mj122333/TSCmikroklima/node/scheme/esp32_pins.PNG

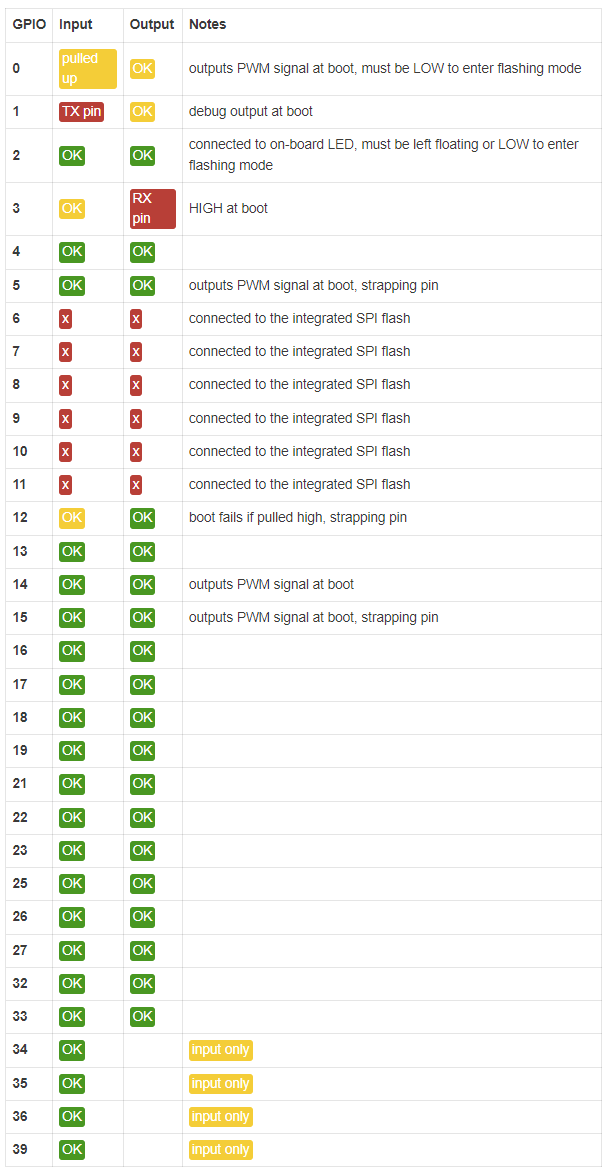
node/scheme/esp32_pins.PNG
