mj122333/TSCmikroklima/node/scheme/komponente/18b20.PNG

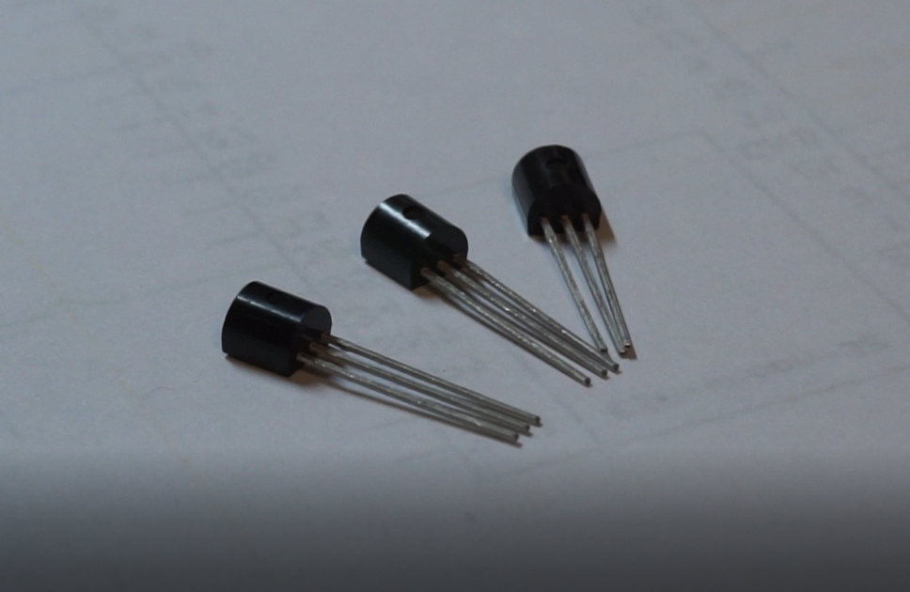
node/scheme/komponente/18b20.PNG
