mj122333/TSCmikroklima/node/scheme/komponente/baterija_18650.PNG

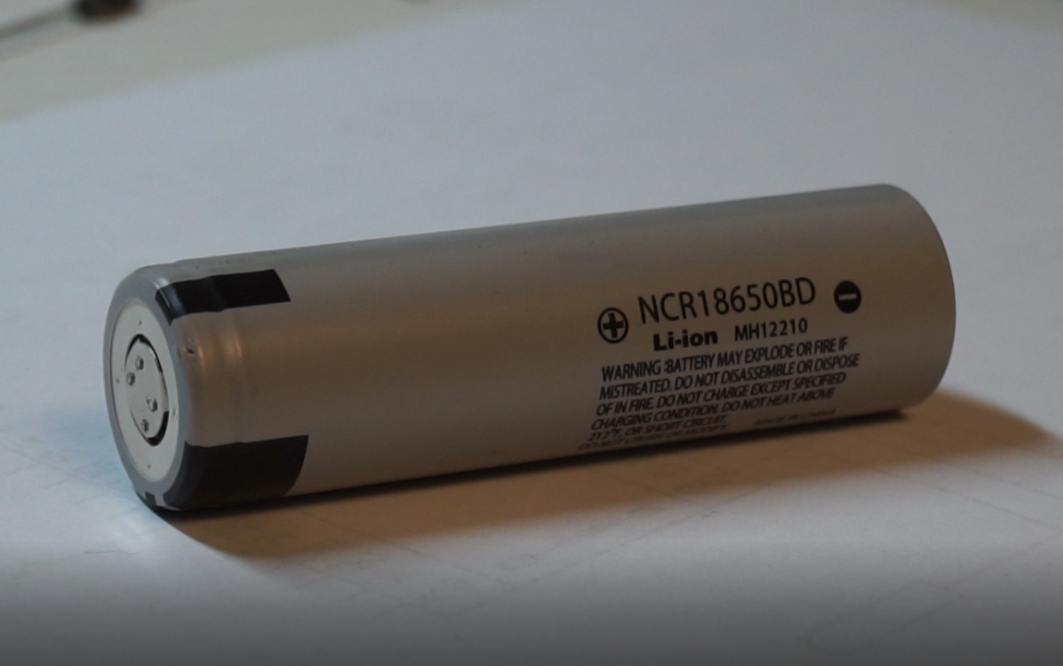
node/scheme/komponente/baterija_18650.PNG
