mj122333/TSCmikroklima/node/scheme/komponente/dioda.PNG

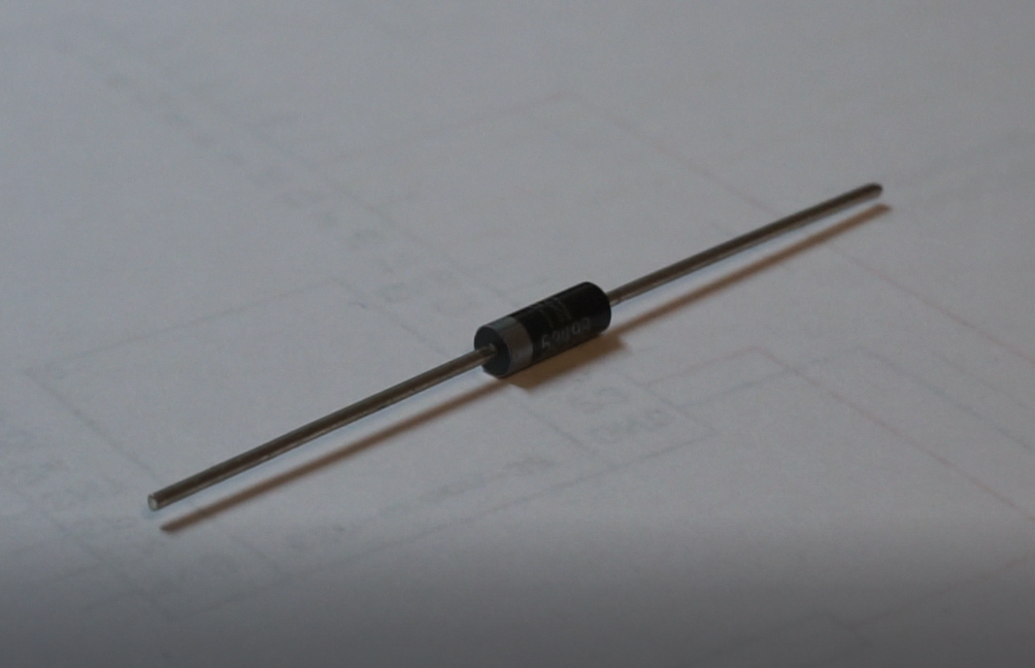
node/scheme/komponente/dioda.PNG
