mj122333/TSCmikroklima/node/scheme/komponente/esp32.PNG

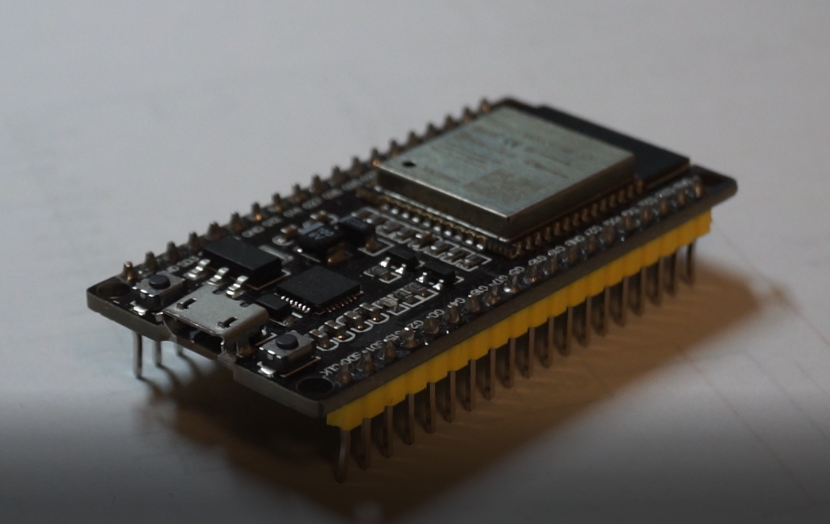
node/scheme/komponente/esp32.PNG
