mj122333/TSCmikroklima/node/scheme/komponente/hall.PNG

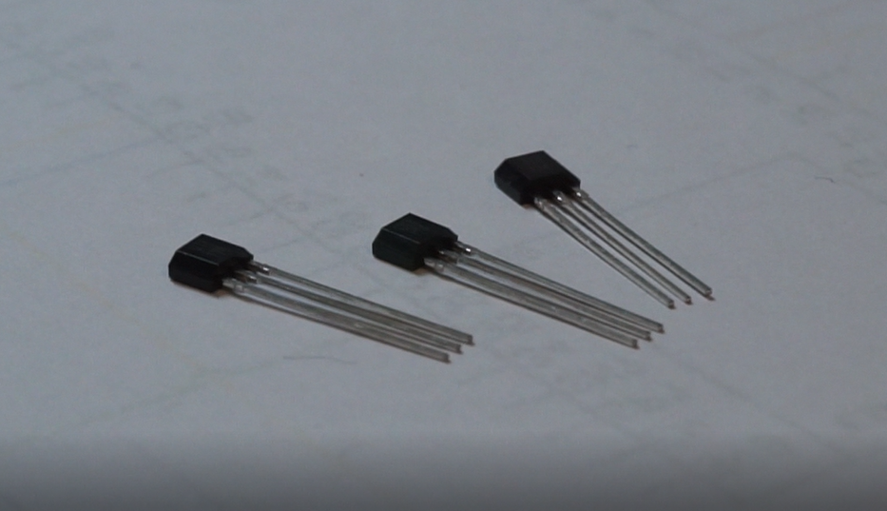
node/scheme/komponente/hall.PNG
