mj122333/TSCmikroklima/node/scheme/komponente/hall_u_akciji.PNG

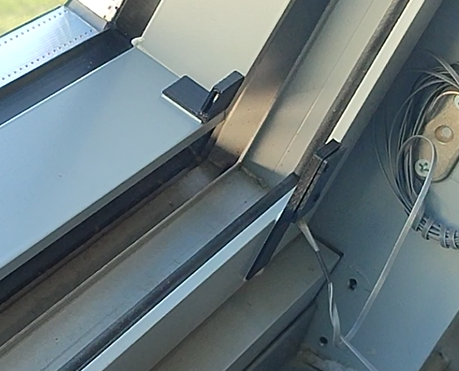
node/scheme/komponente/hall_u_akciji.PNG
