mj122333/TSCmikroklima/node/scheme/komponente/kuciste.PNG

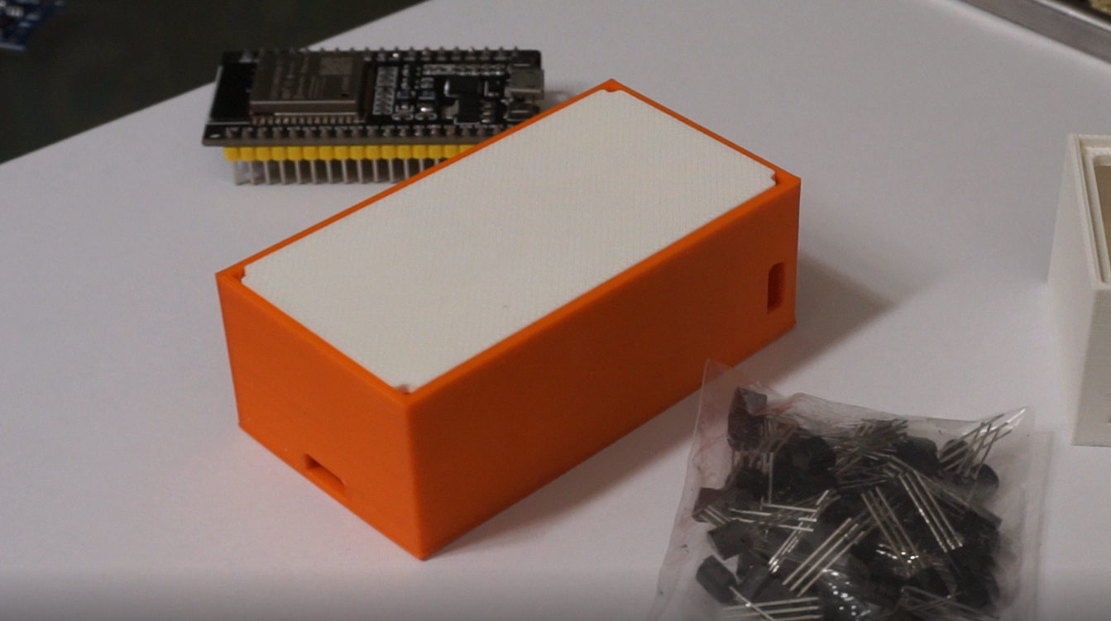
node/scheme/komponente/kuciste.PNG
