mj122333/TSCmikroklima/node/scheme/komponente/otpornici.PNG

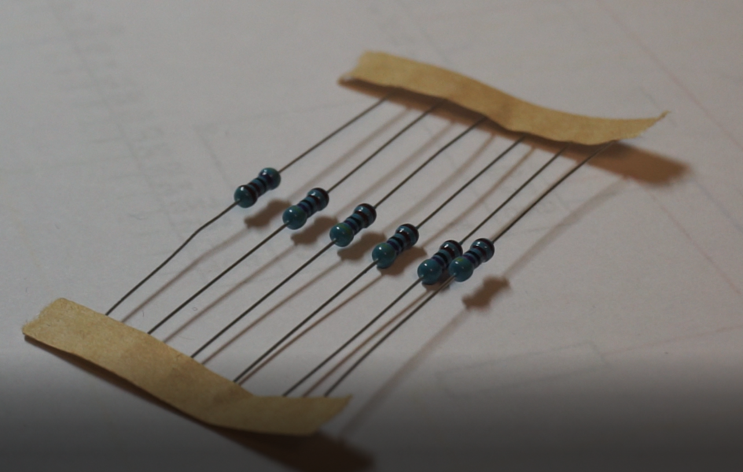
node/scheme/komponente/otpornici.PNG
