mj122333/TSCmikroklima/node/scheme/komponente/punjac.PNG

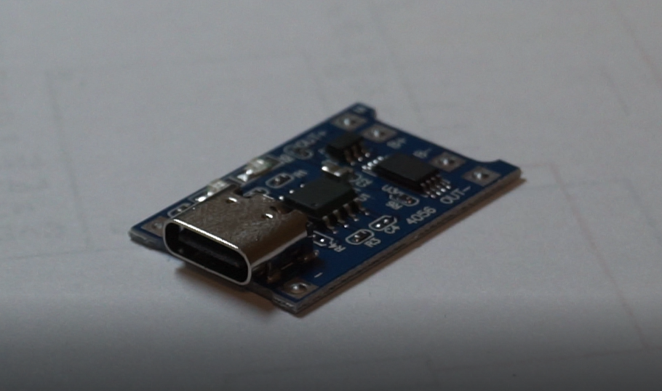
node/scheme/komponente/punjac.PNG
