mj122333/TSCmikroklima/node/scheme/scheme_3_2.PNG

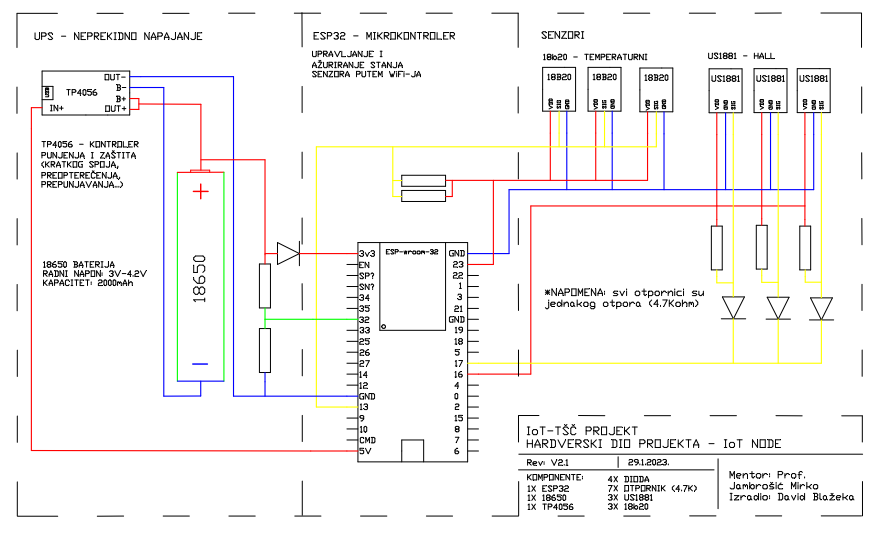
node/scheme/scheme_3_2.PNG
