mj122333/TSCmikroklima/node/scheme/underside_pinView.jpg

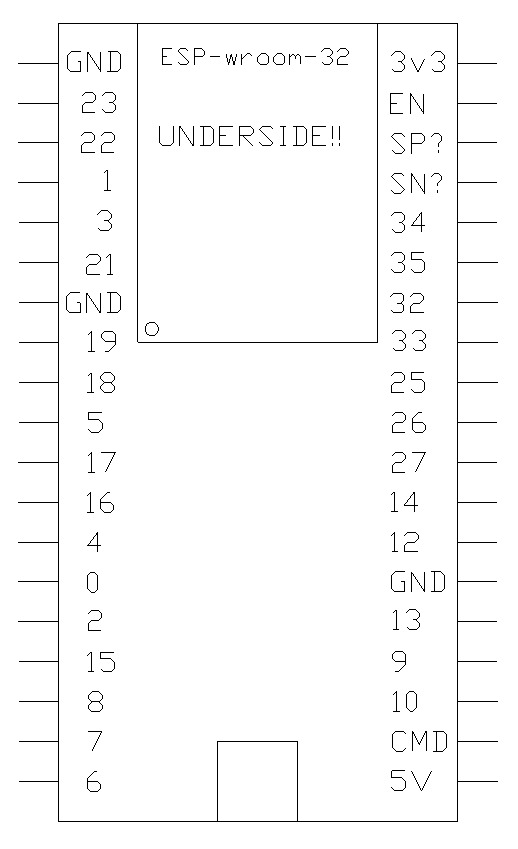
node/scheme/underside_pinView.jpg
