mj122333/TSCmikroklima/server/slike/tlocrt-kat-hodnik-tv.png

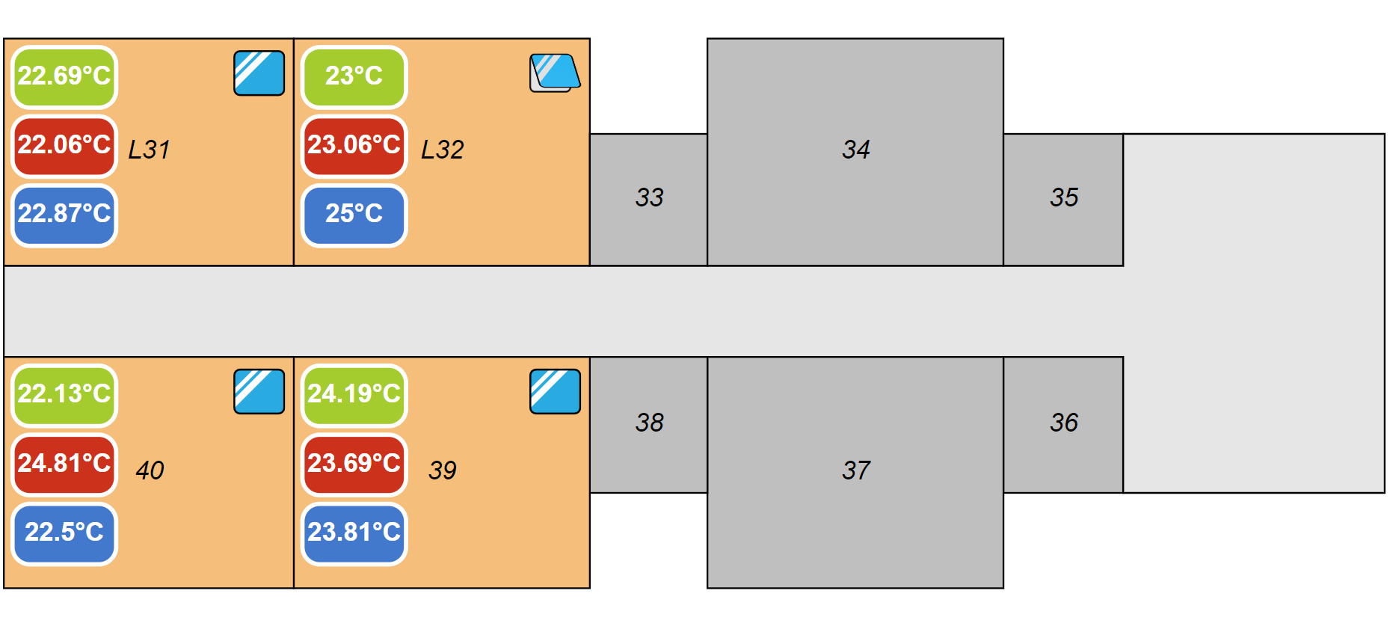
server/slike/tlocrt-kat-hodnik-tv.png
