mj122333/TSCmikroklima/server/slike/tlocrt-kat-tv.png

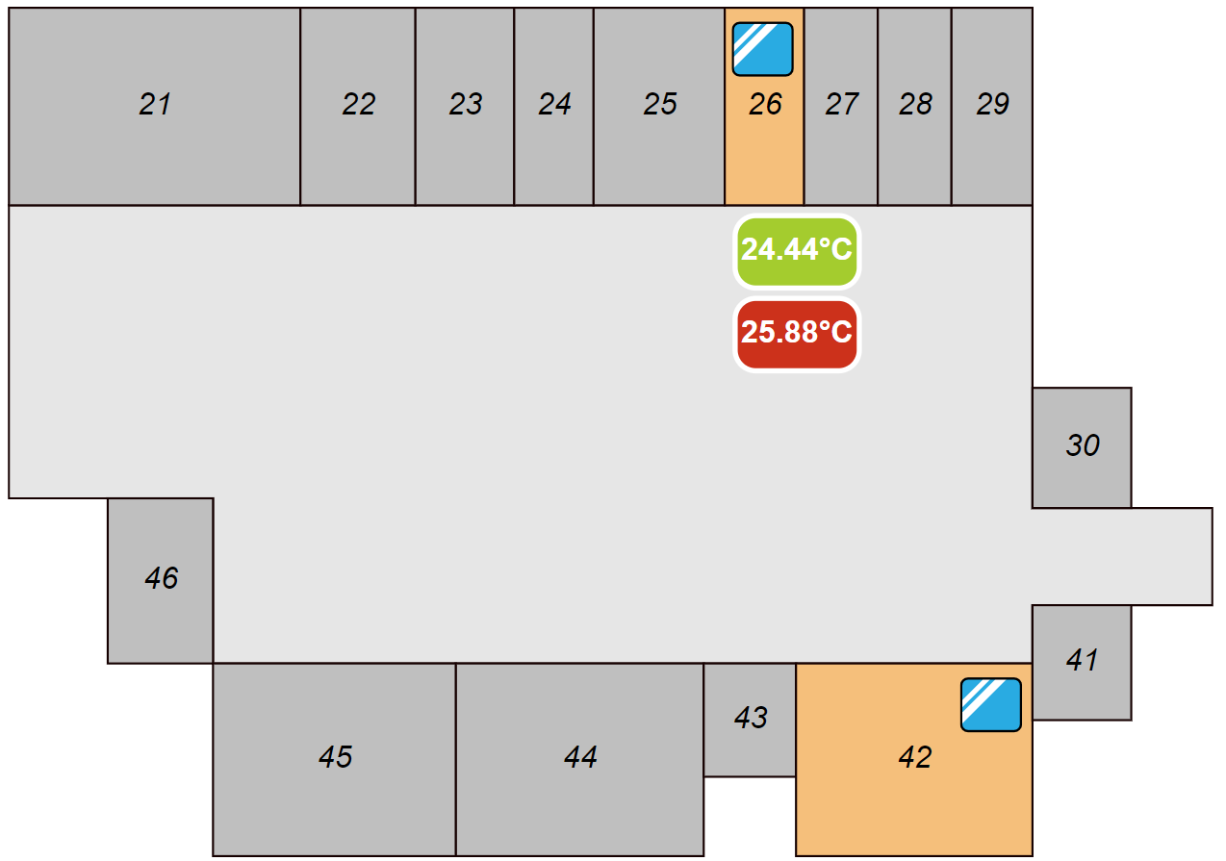
server/slike/tlocrt-kat-tv.png
