mj122333/TSCmikroklima/server/slike/tlocrt-kat.png

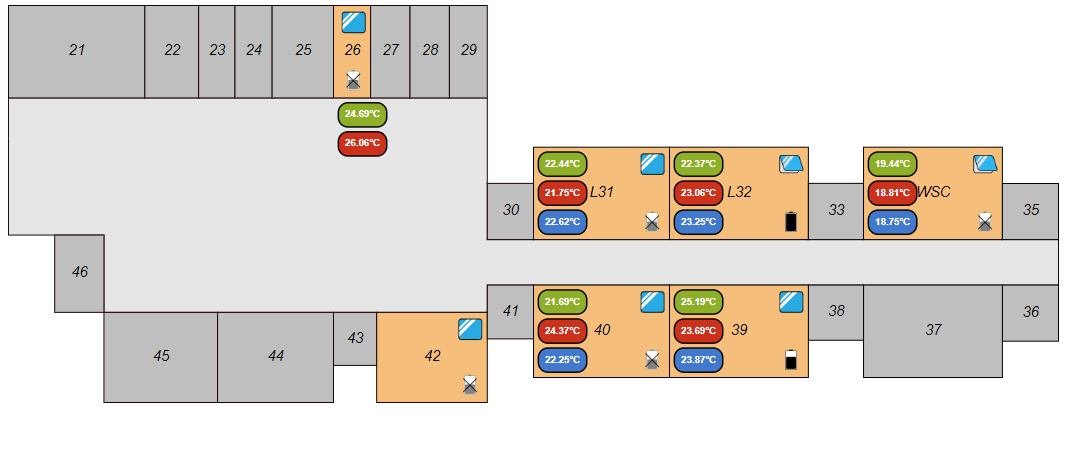
server/slike/tlocrt-kat.png
