mj122333/TSCmikroklima/server/slike/tlocrt-prizemlje-hodnik-tv.png

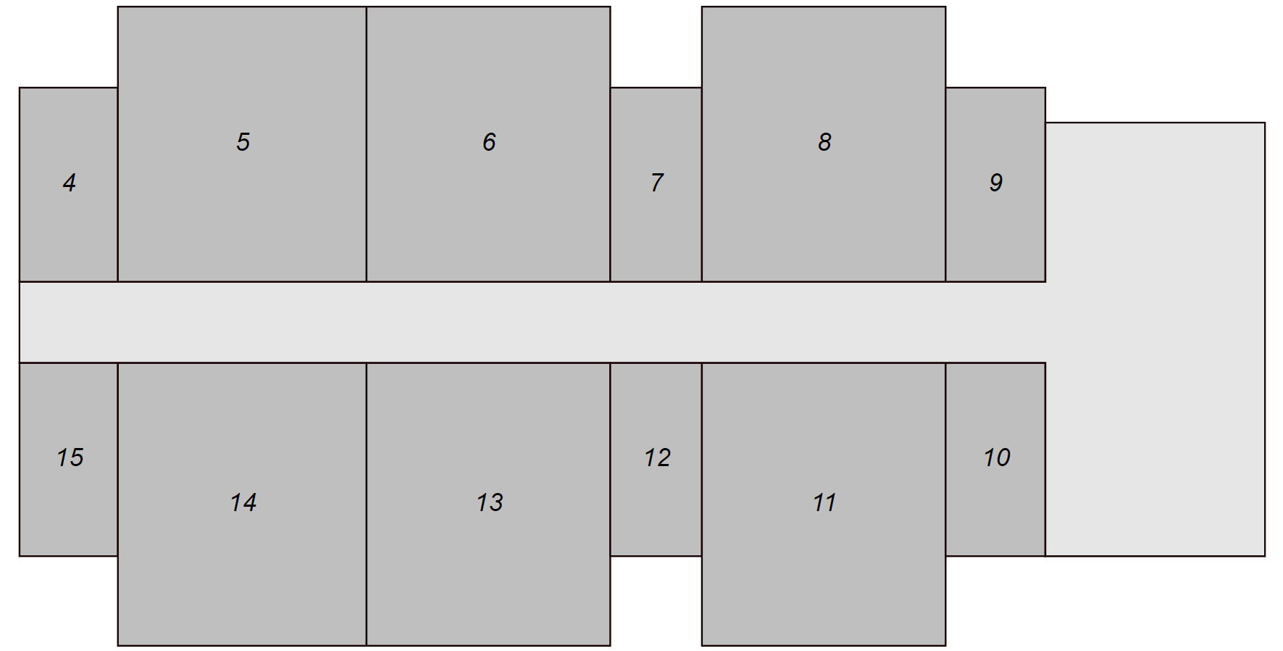
server/slike/tlocrt-prizemlje-hodnik-tv.png
