mj122333/TSCmikroklima/server/slike/tlocrt-prizemlje.png

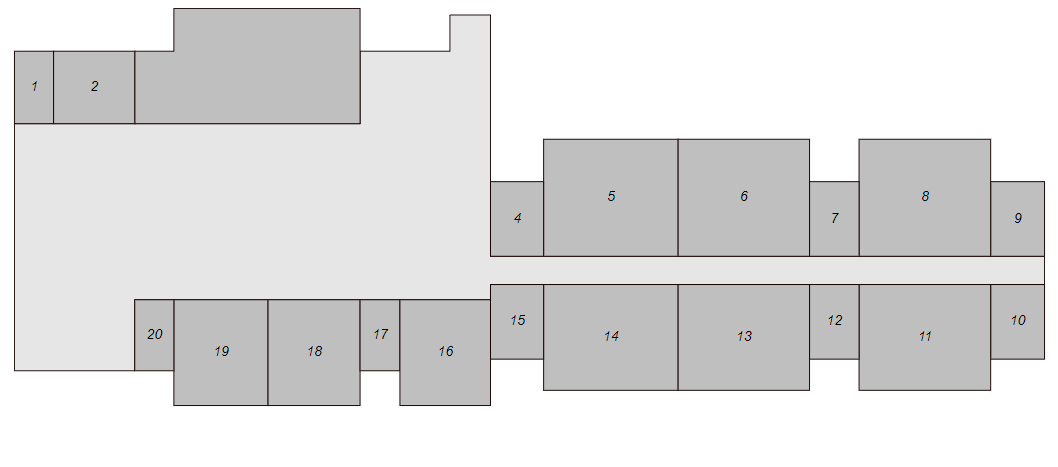
server/slike/tlocrt-prizemlje.png
