mj122333/TSCmikroklima/node/3D_printing/step_files_blend/18b20_mount_radijator.STEP

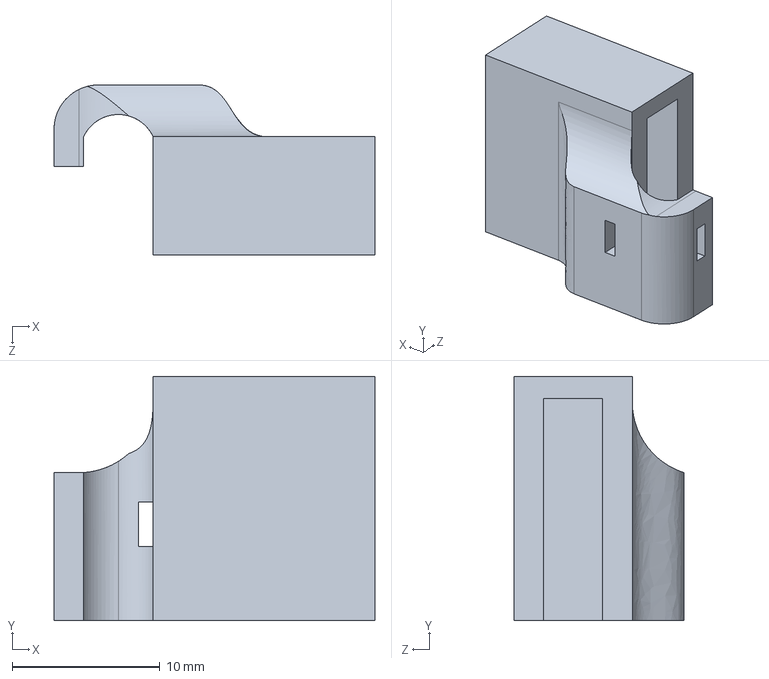
[picture p34: CAD file, 2023-02-15]
node/3D_printing/step_files_blend/18b20_mount_radijator.STEP
21.7 x 16.5 x 11.5 mm
