mj122333/TSCmikroklima/node/3D_printing/tablet/tablet_holder2.SLDPRT

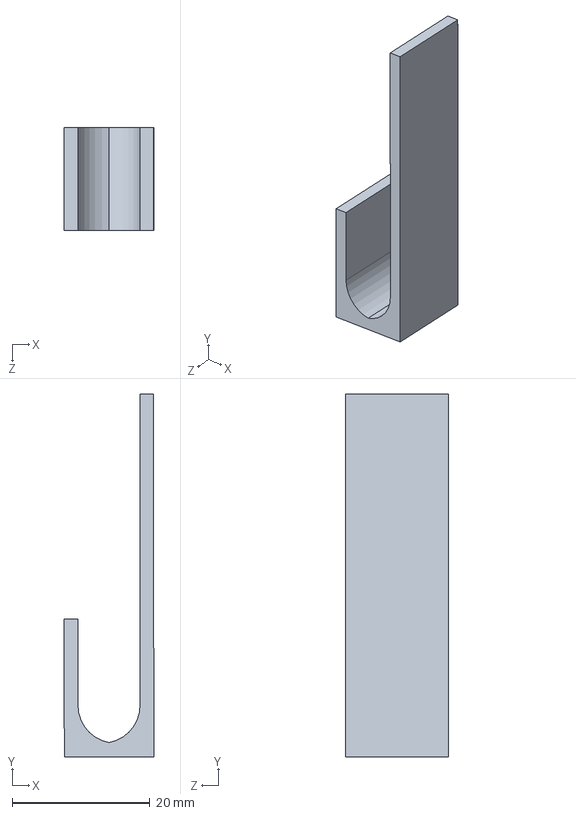
[picture p35: CAD file, 2023-05-17]
node/3D_printing/tablet/tablet_holder2.SLDPRT
13.0 x 52.7 x 15.0 mm
