mj122333/TSCmikroklima/node/scheme/nanoCAD/esp32_schem.dxf

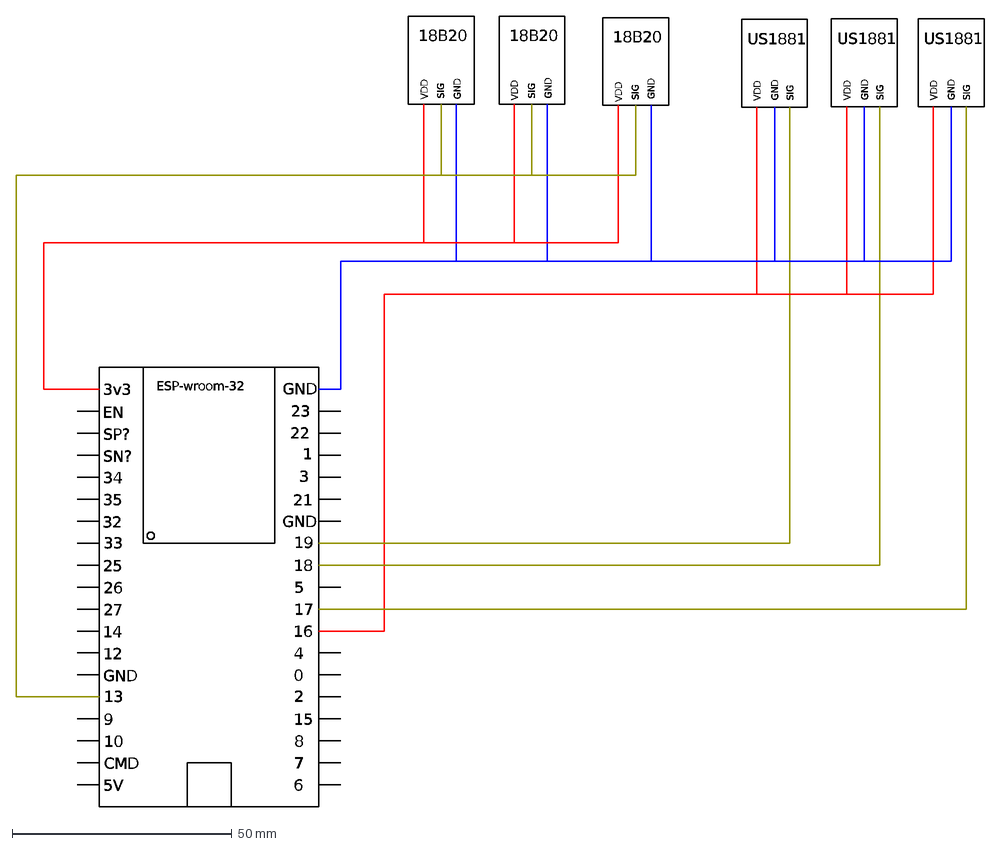
[picture p36: CAD file, 2023-01-26]
node/scheme/nanoCAD/esp32_schem.dxf
3v3
SP?
SN?
34
35
EN
32
33
26
27
14
12
25
GND
13
10
CMD
5V
9
22
1
3
21
23
19
5
17
16
4
18
0
2
8
7
6
15
ESP-wroom-32
18B20
US1881
SIG
VDD
