mj122333/TSCmikroklima/node/3D_printing/3D_component_models/charge_controller.SLDPRT

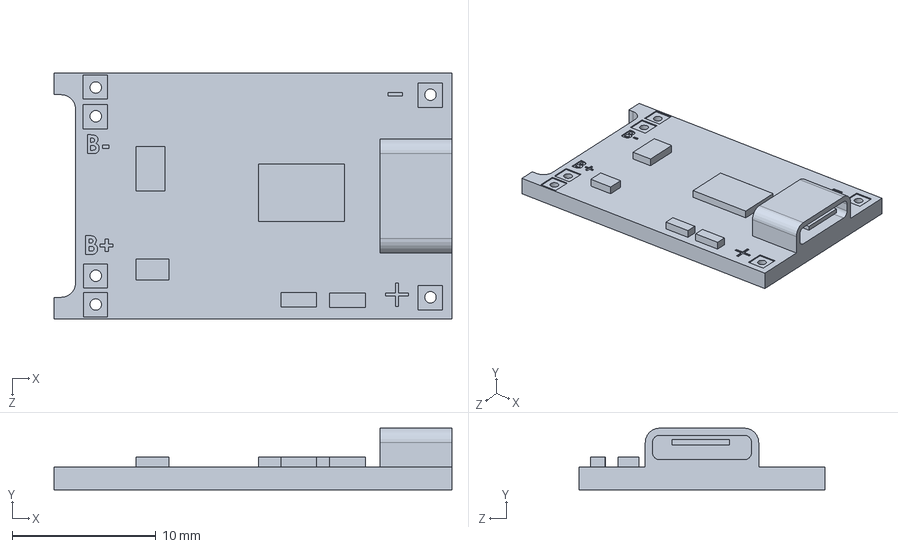
[picture p37: CAD file, 2023-01-26]
node/3D_printing/3D_component_models/charge_controller.SLDPRT
27.7 x 4.30 x 17.1 mm
