mj122333/TSCmikroklima/node/3D_printing/senzori_kucista/magnet_mount.SLDPRT

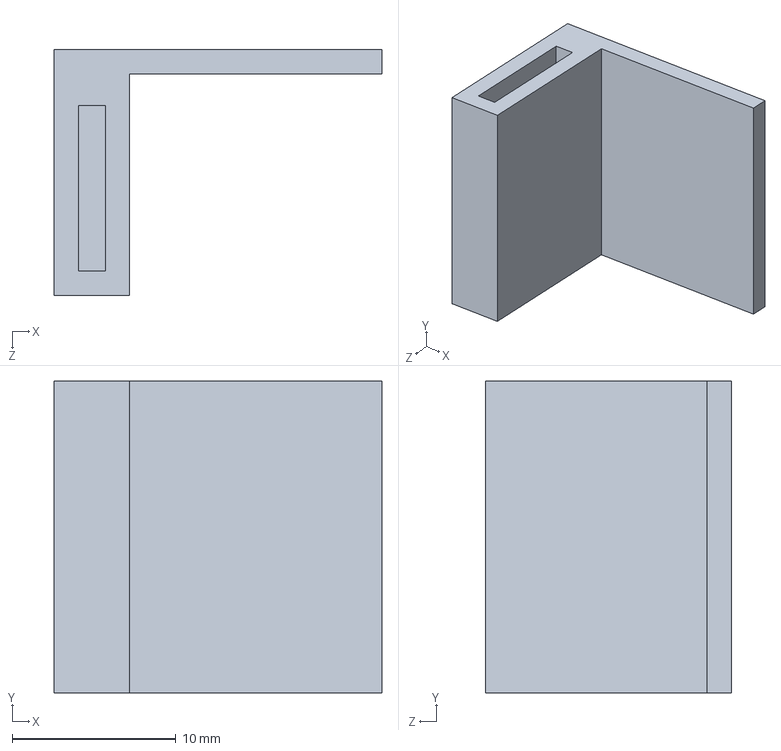
[picture p38: CAD file, 2023-02-15]
node/3D_printing/senzori_kucista/magnet_mount.SLDPRT
20.0 x 19.0 x 15.0 mm
