mj122333/TSCmikroklima/node/3D_printing/step_files_blend/ESP32_model.STEP

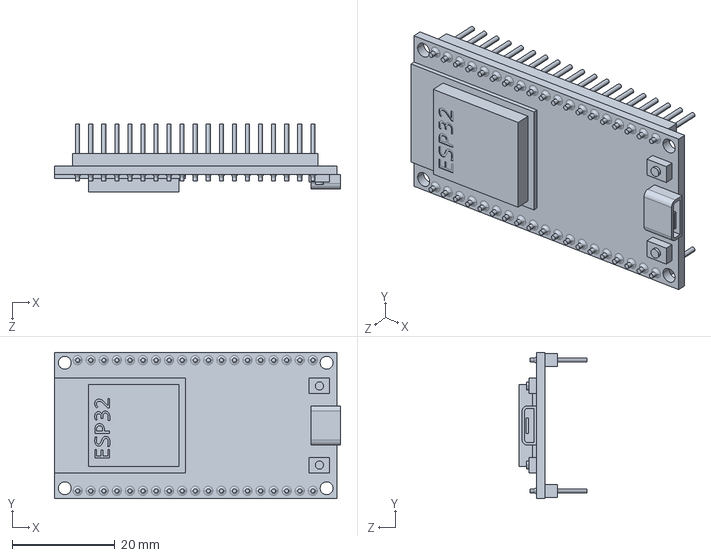
[picture p39: CAD file, 2023-02-15]
node/3D_printing/step_files_blend/ESP32_model.STEP
55.6 x 28.4 x 13.2 mm
