mj122333/TSCmikroklima/node/3D_printing/tablet/tablet_holder.SLDPRT

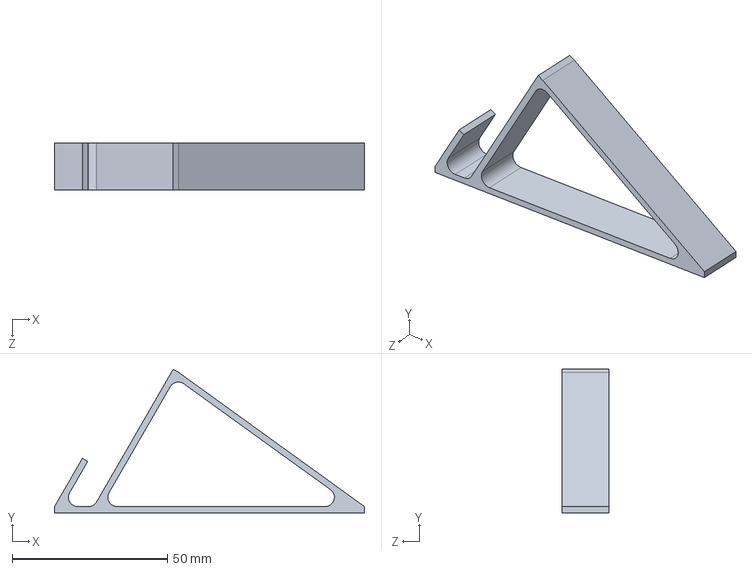
[picture p40: CAD file, 2023-05-09]
node/3D_printing/tablet/tablet_holder.SLDPRT
100.0 x 46.3 x 15.0 mm
