mj122333/TSCmikroklima/node/3D_printing/3D_printing_stl/hall_mount_zaProzor_kutijica.STL

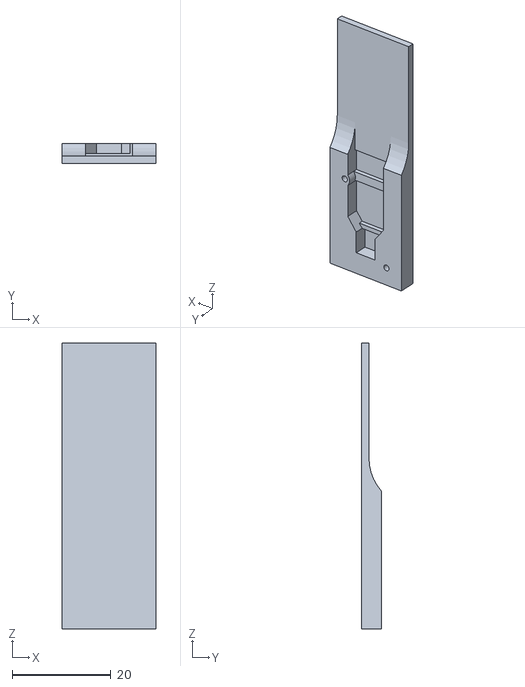
[picture p41: CAD file, 2023-02-15]
node/3D_printing/3D_printing_stl/hall_mount_zaProzor_kutijica.STL
19.0 x 4.00 x 58.0
