mj122333/TSCmikroklima/node/3D_printing/senzori_kucista/hall_mount_zaProzor_poklopac.SLDPRT

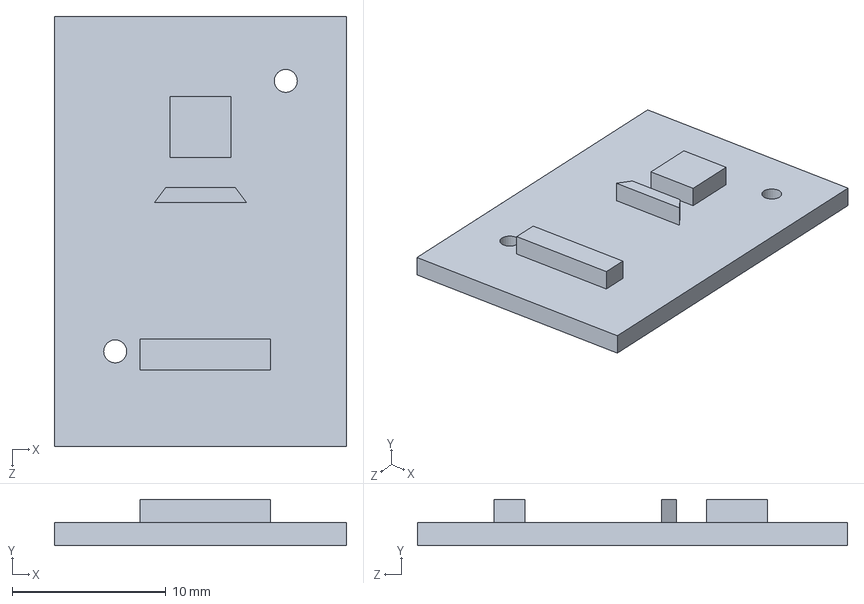
[picture p42: CAD file, 2023-02-15]
node/3D_printing/senzori_kucista/hall_mount_zaProzor_poklopac.SLDPRT
19.0 x 3.00 x 28.0 mm
