mj122333/TSCmikroklima/node/3D_printing/3D_printing_stl/18b20_mount_radijator.STL

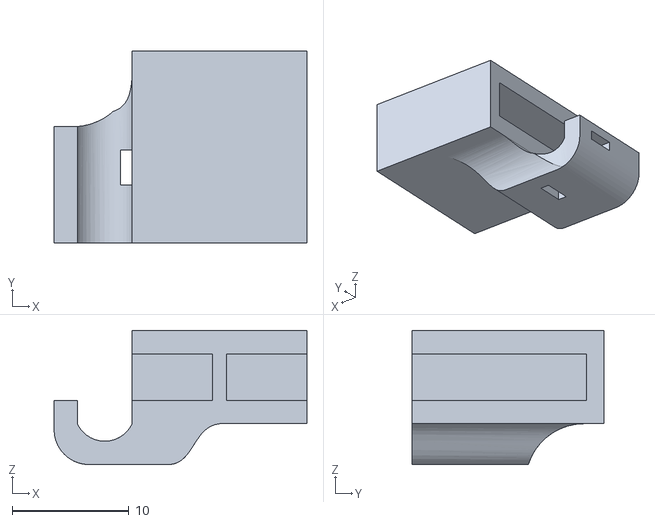
[picture p43: CAD file, 2023-01-31]
node/3D_printing/3D_printing_stl/18b20_mount_radijator.STL
21.7 x 16.5 x 11.5
