mj122333/TSCmikroklima/node/3D_printing/slike/asembli_solid_Batt_img1.PNG

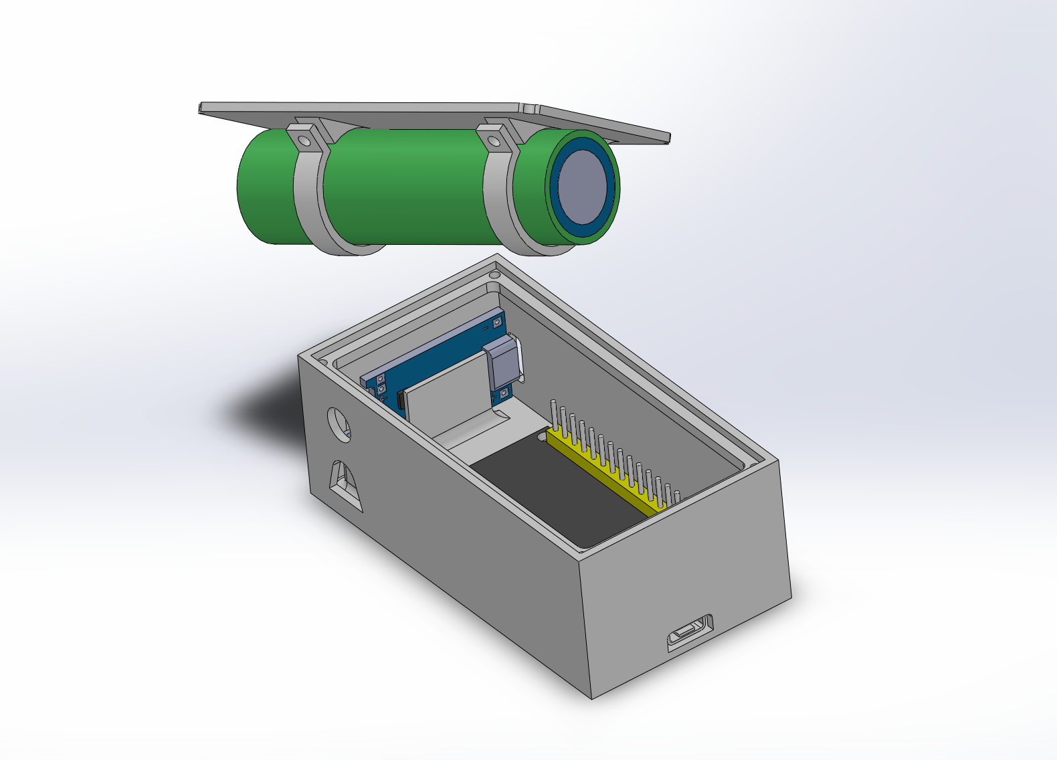
node/3D_printing/slike/asembli_solid_Batt_img1.PNG
