mj122333/TSCmikroklima/node/3D_printing/slike/asembli_solid_Batt_img2.PNG

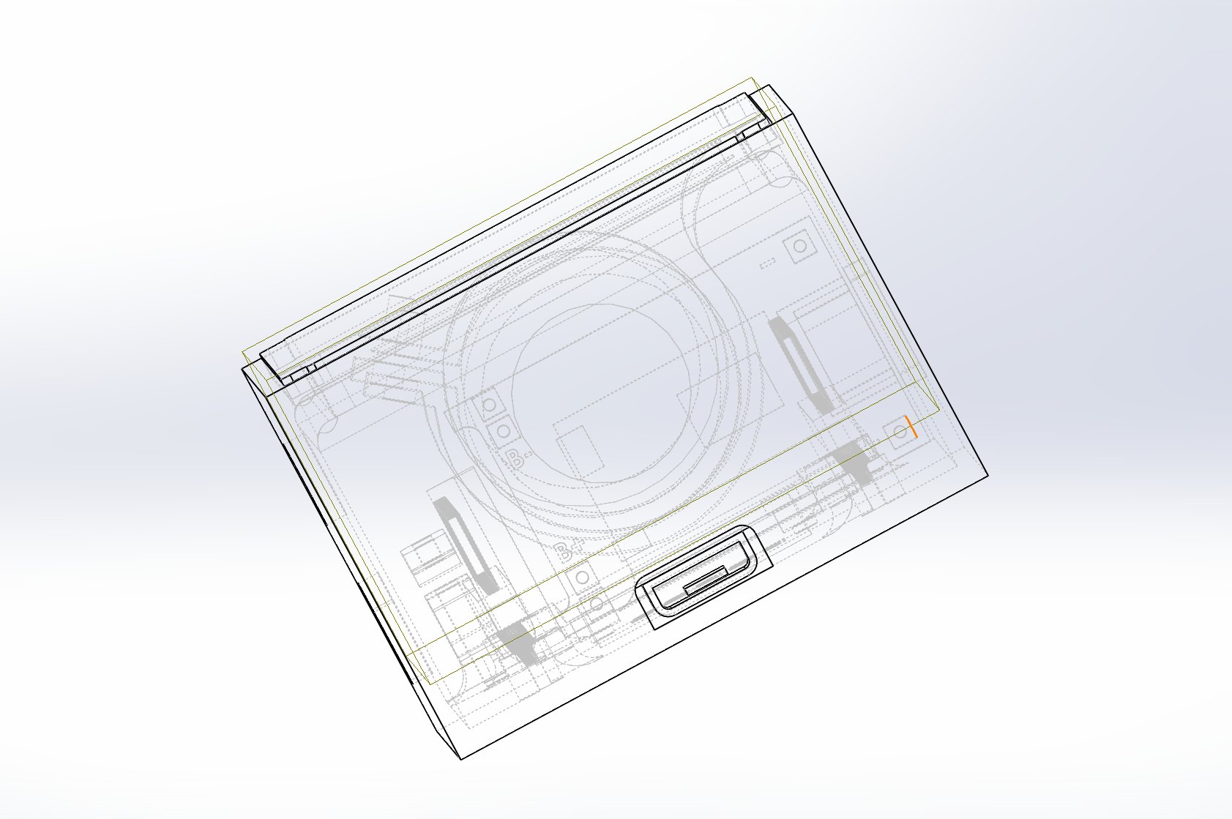
node/3D_printing/slike/asembli_solid_Batt_img2.PNG
