mj122333/TSCmikroklima/node/3D_printing/slike/Batteries_on_2versions_of_lids.PNG

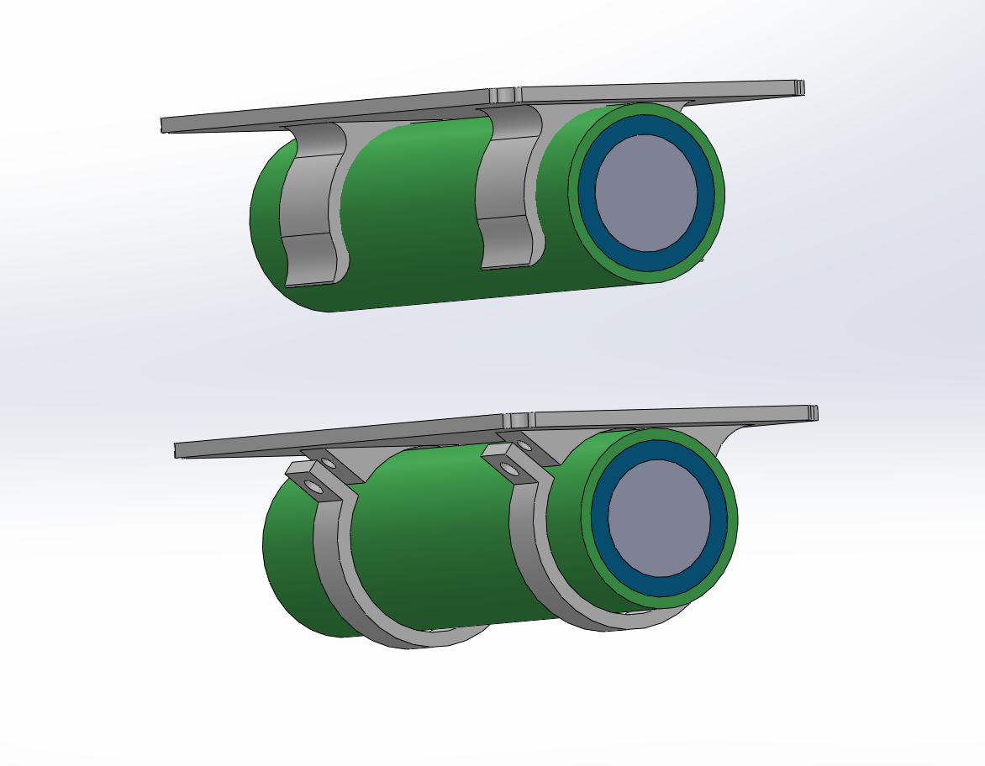
node/3D_printing/slike/Batteries_on_2versions_of_lids.PNG
