mj122333/TSCmikroklima/node/3D_printing/slike/battery_model_img.PNG

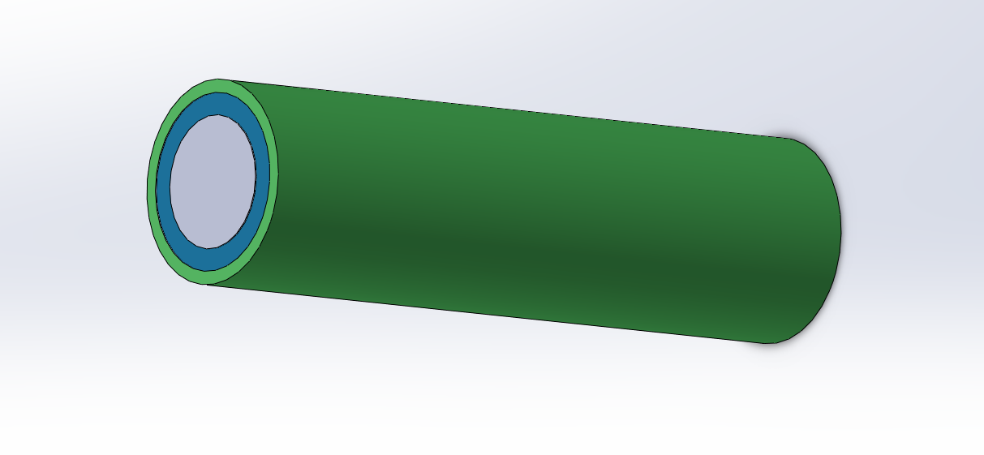
node/3D_printing/slike/battery_model_img.PNG
