mj122333/TSCmikroklima/node/3D_printing/slike/charge_controller_img.PNG

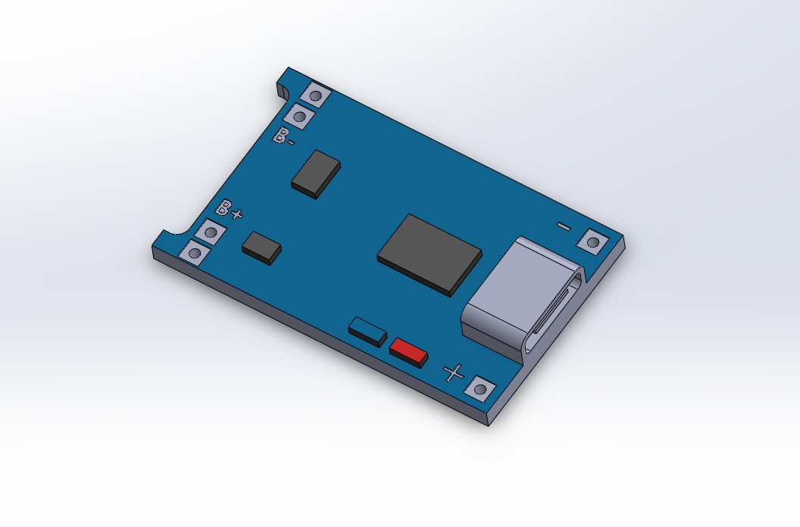
node/3D_printing/slike/charge_controller_img.PNG
